mekeetsa/gp40/LTspice_SD_interface/SD_interface.png

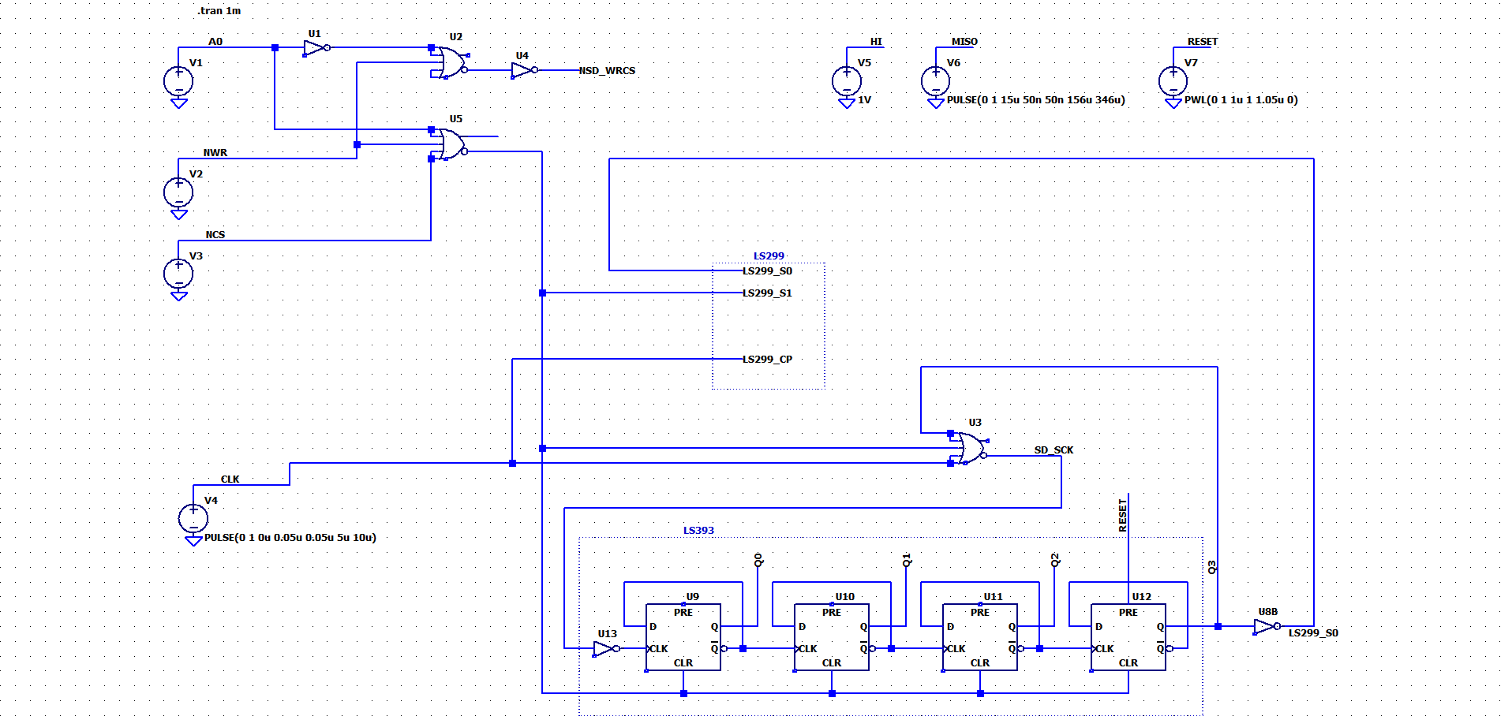
LTspice_SD_interface/SD_interface.png
