mekeetsa/gp40/LTspice_composite_video/composite_video_LPF_results.png

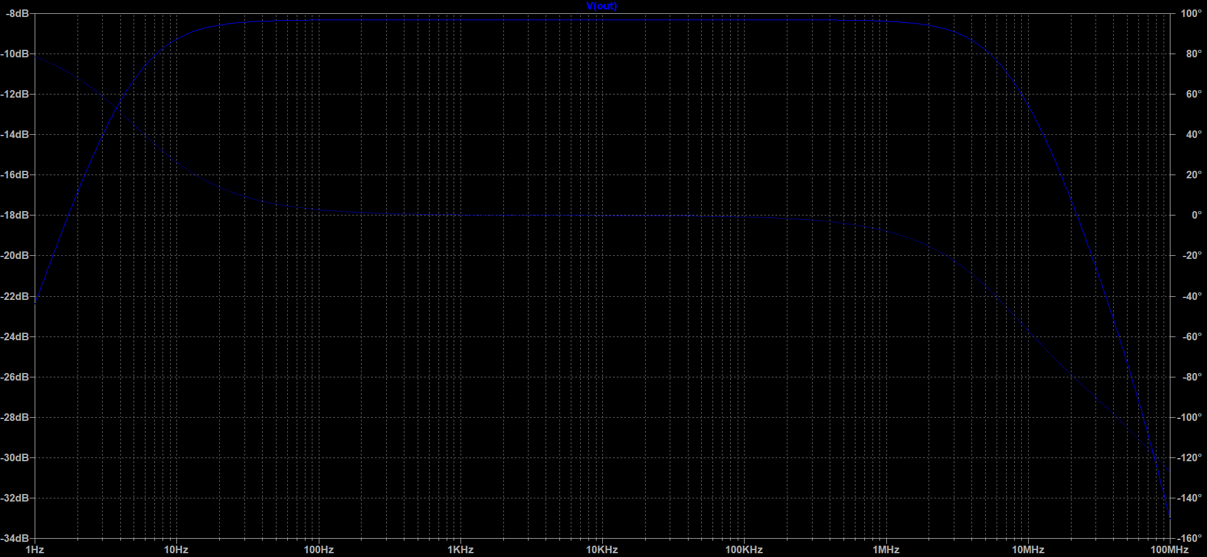
LTspice_composite_video/composite_video_LPF_results.png
