mekeetsa/gp40/LTspice_composite_video/composite_video_results.png

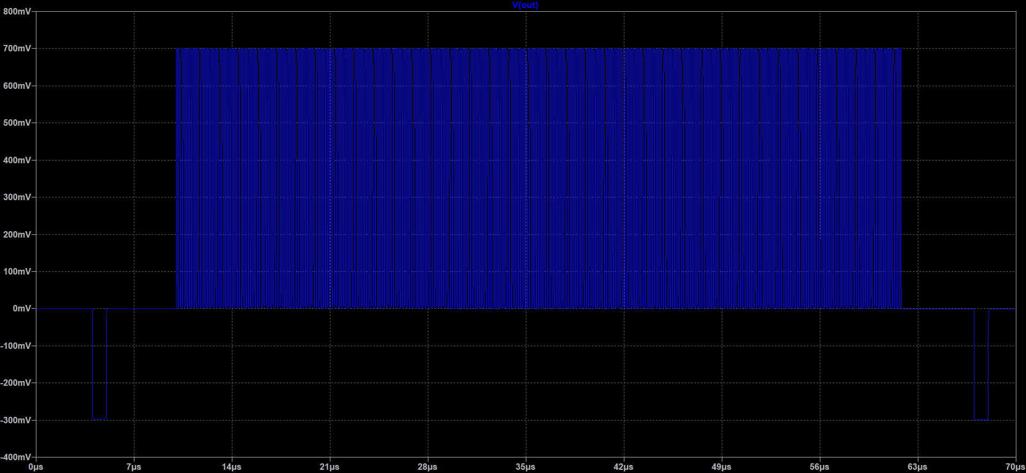
LTspice_composite_video/composite_video_results.png
