mekeetsa/gp40/LTspice_SD_interface/SD_interface_results.png

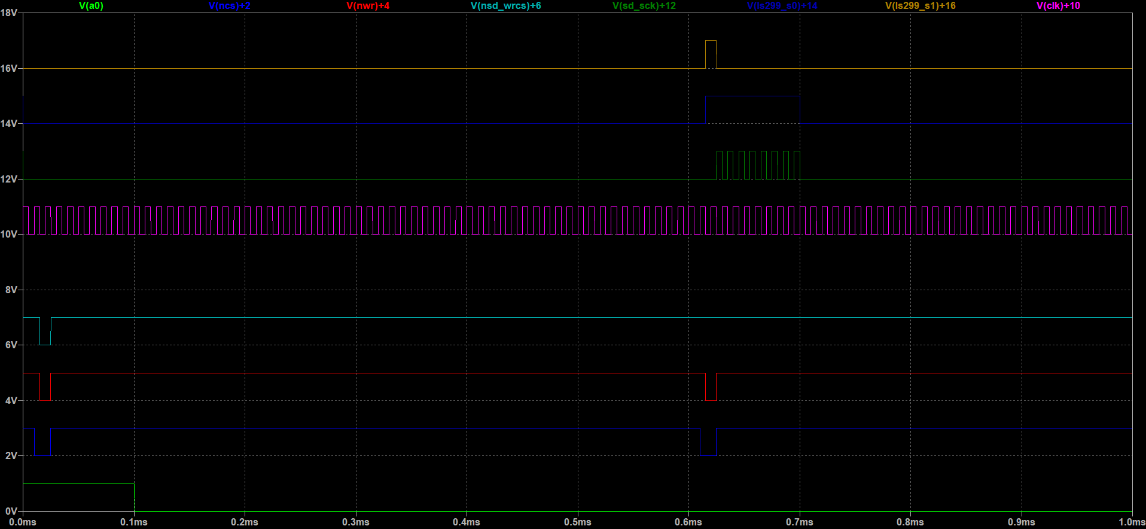
LTspice_SD_interface/SD_interface_results.png
