mekeetsa/gp40/LTspice_composite_video/composite_video.asc

C1: cap; 220µF
C2: cap; 100pF
D1: diode; BAT54
D2: diode; BAT54
Q1: npn; BFR183
R1: res; 62R
R2: res; 4.3k
R3: res; 750R
R4: res; 1k
R5: res; 1k
R6: res; 100R
R7: res; 1R
R8: res; 180R
R9: res; 1R
R10: res; 100R
Rout: res; 75R
Rt1: res; 1mR
Rt2: res; 100Meg
V1: voltage; 5V
V2: voltage; PULSE(0.2 3 4u 10n 10n 1u 63u)
V3: voltage; PULSE(3 0 10u 10n 10n 82n 162n 320)
V4: voltage; PULSE(3 0 73u 10n 10n 82n 162n 320)
Named nets: 0, A, Y, VCC, S, B, OUT
.tran 150u
.INCLUDE library.cir
Rout = 75k yields 2 Vpp across R11
Rout = 75R yields 1 Vpp across R11
Conculsion: Zout = 75R
X2 S B B VCC 0 SN7438
X1 Y A A VCC 0 SN7438
