mekeetsa/gp40/LTspice_composite_video/composite_video_LPF.asc

C1: cap; 220µF
C2: cap; 560pF
Q1: npn; BFR183
R1: res; 62R
R2: res; 4.3k
R4: res; 1k
R5: res; 750R
R8: res; 180R
Rout: res; 75R
Rt1: res; 1mR
Rt2: res; 100Meg
V1: voltage; 5V
V2: voltage; 2.4; AC 2.2; Rser=10
Named nets: 0, VCC, OUT
.op
.ac dec 100 1 100Meg
; .tran 1u
.INCLUDE library.cir
