mekeetsa/gp40/LTspice_SD_interface/SD_interface.asc

U1: inv; td=50n
U2: or; td=50n
U3: or; td=50n
U4: inv; td=50n
U5: or; td=50n
U8B: inv; td=50n
U9: dflop; td=50n
U10: dflop; td=50n
U11: dflop; td=50n
U12: dflop; td=50n
U13: inv; td=50n
V1: voltage; PWL(0 1 101u 1 101.05u 0)
V2: voltage; PWL(0 1 15u 1 15.05u 0 20u 0 25u 0 25.05u 1 615u 1 615.05u 0 620u 0 625u 0 625.05u 1)
V3: voltage; PWL(0 1 10u 1 10.05u 0 20u 0 25u 0 25.05u 1 610u 1 610.05u 0 620u 0 625u 0 625.05u 1)
V4: voltage; PULSE(0 1 0u 0.05u 0.05u 5u 10u)
V5: voltage; 1V
V6: voltage; PULSE(0 1 15u 50n 50n 156u 346u)
V7: voltage; PWL(0 1 1u 1 1.05u 0)
Named nets: 0, A0, NWR, NCS, CLK, HI, SD_SCK, LS299_CP, LS299_S1, Q0, Q1, Q2, Q3, MISO, RESET, NSD_WRCS, LS299_S0
.tran 1m
LS299
LS393
